mod-audio/cc-hw-footswitch/MOD_Foot_Prototype1/control-chain.sch

## KiCad design MOD_Foot_Prototype1/control-chain.sch (2014-12-17)

Schematic: control-chain.sch

Parts:
C5: 100uF; CAP_RAD_5MM
C8, C18: 100nF_X7R; SM0603
D2, D3: MMSZ5242B; SOD123
J1: RJ45_CHAIN_MAIN; RJ45-RJHSE5084
J2: RJ45_CHAIN_EXTENSION; RJ45-RJHSE5084
Q1: MMBT3904; SOT23
Q2: MMBT3906; SOT23
R1, R27: 1k; SM0603
R2, R11: 100R 0.5W; SM1210
R3, R4, R5, R6: 470R; SM0805
R12: 100k; SM0603
R13, R28, R29, R30, R31: 10k; SM0603
R44: 0R/NC; SM0805
U4: MAX13450E; TSSOP14

Notes on the sheet:
PCB consideration: This capacitor must be placed as close as possible to the IC
