mod-audio/cc-hw-footswitch/MOD_Foot_Prototype1/cpu.sch

## KiCad design MOD_Foot_Prototype1/cpu.sch (2014-12-16)

Schematic: cpu.sch

Parts:
C9, C12, C13: 100nF_X7R; SM0603
C10, C11: 18pF_NP0; SM0603
CN1, CN2: CONN_PANNEL_2X2; CONN_PANNEL
P1, P2: HEADER_5X2; PIN_ARRAY_5x2
R32, R33, R46, R47: 10k; SM0603
R39, R42, R43, R45: 0R; SM0805
R40, R41: 100R; SM0603
U1: LPC111X_LQFP48; LQFP48
X1: 10MHz; HC_49US
