mod-audio/cc-hw-footswitch/MOD_Foot_Prototype1/display.sch

## KiCad design MOD_Foot_Prototype1/display.sch (2014-12-16)

Schematic: display.sch

Parts:
C14, C15, C17: 100nF_X7R; SM0603
C16: 100uF; CAP_RAD_5MM
LCD1: AGM-2004A-204; LCD-AGM-2004A-204
Q3: MMBT3904; SOT23
R34: 3k; SM0805
R35: 330R; SM0805
R36: 1k; SM0603
R37: 0R; SM0805
U5, U6: 74HC245; TSSOP20
