mod-audio/cc-hw-footswitch/MOD_Foot_Prototype1/io.sch

## KiCad design MOD_Foot_Prototype1/io.sch (2014-12-16)

Schematic: io.sch

Parts:
FOOT1, FOOT2, FOOT3, FOOT4: HEADER_2X1_180; PIN_ARRAY_2X1
LED1, LED2, LED3, LED4: LED_RGB; LED_CLRTB_GFSF_1
R7, R8, R9, R10: 10k; SM0603
R14, R15, R16, R17, R18, R19, R20, R21, R22, R23, R24, R25: 1k; SM0603
