mod-audio/cc-hw-footswitch/MOD_Foot_Prototype1/power.sch

## KiCad design MOD_Foot_Prototype1/power.sch (2014-12-16)

Schematic: power.sch

Parts:
C1, C3, C6: 100uF; CAP_RAD_5MM
C2, C4, C7: 100nF_X7R; SM0603
D1: CGRA4007-G; DO-214AC(SMA)
R26, R38: 0R; SM0805
RT1: PTC_FUSE_500mA; SM2920
RT2: PTC_FUSE_500mA; SM1210
TP1, TP2, TP3: CONN_1; SIL-1
U2: MC7805; DPAK(369C)
U3: NCP1117DT33G; DPAK(369C)
